AmbassadorDoge/notakeeb/PCB/marbastlib-main/resources/repolist.png

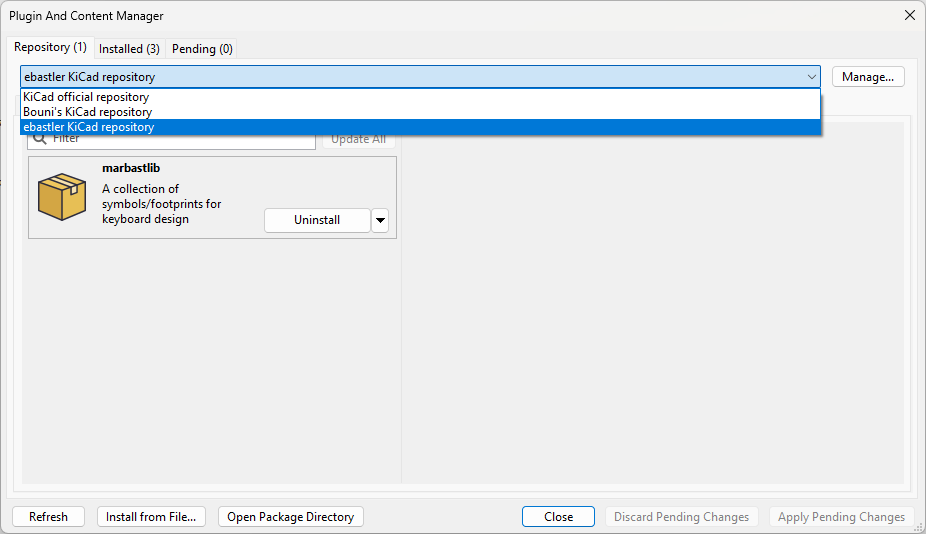
PCB/marbastlib-main/resources/repolist.png
