AmbassadorDoge/notakeeb/PCB/scottokeebs-main/Extras/ScottoModules/STM32F072CBT6/meta/matrix.png

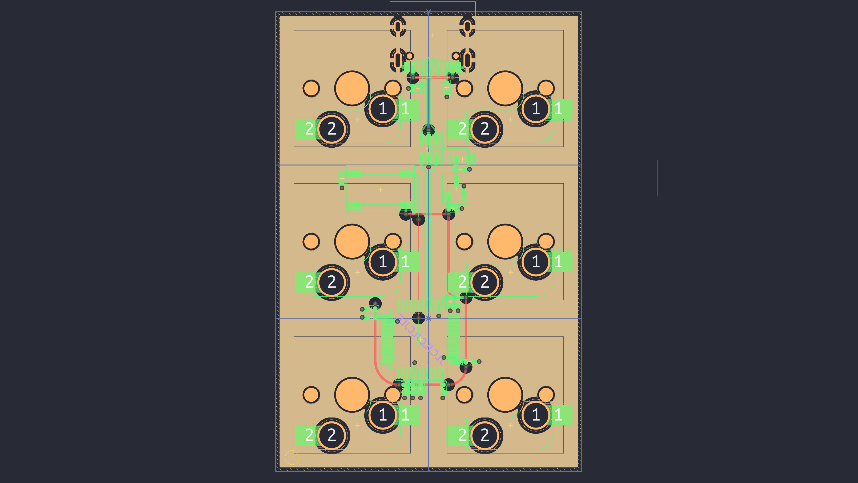
PCB/scottokeebs-main/Extras/ScottoModules/STM32F072CBT6/meta/matrix.png
