AmbassadorDoge/notakeeb/PCB/scottokeebs-main/Extras/ScottoModules/STM32F072CBT6/meta/scottomodules.png

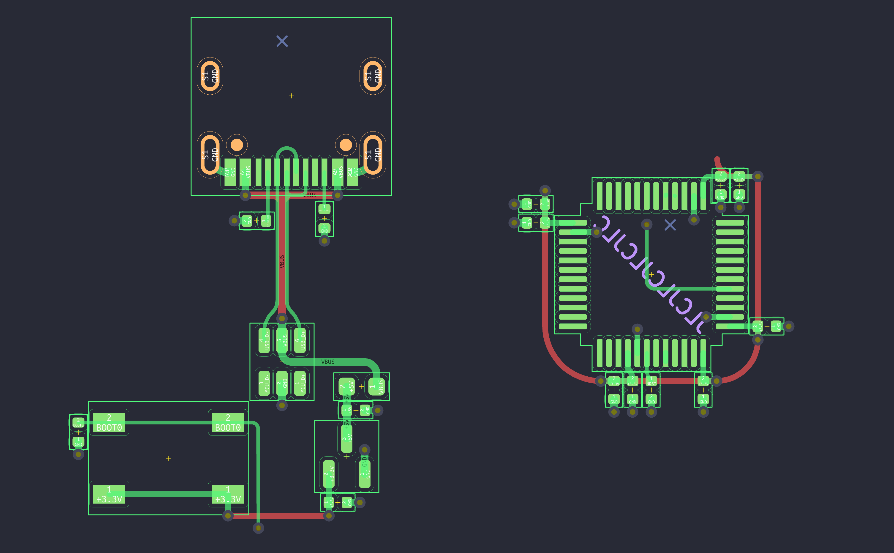
PCB/scottokeebs-main/Extras/ScottoModules/STM32F072CBT6/meta/scottomodules.png
