AmbassadorDoge/notakeeb/PCB/scottokeebs-main/ScottoFrog/Firmware/scottofrog.jpg

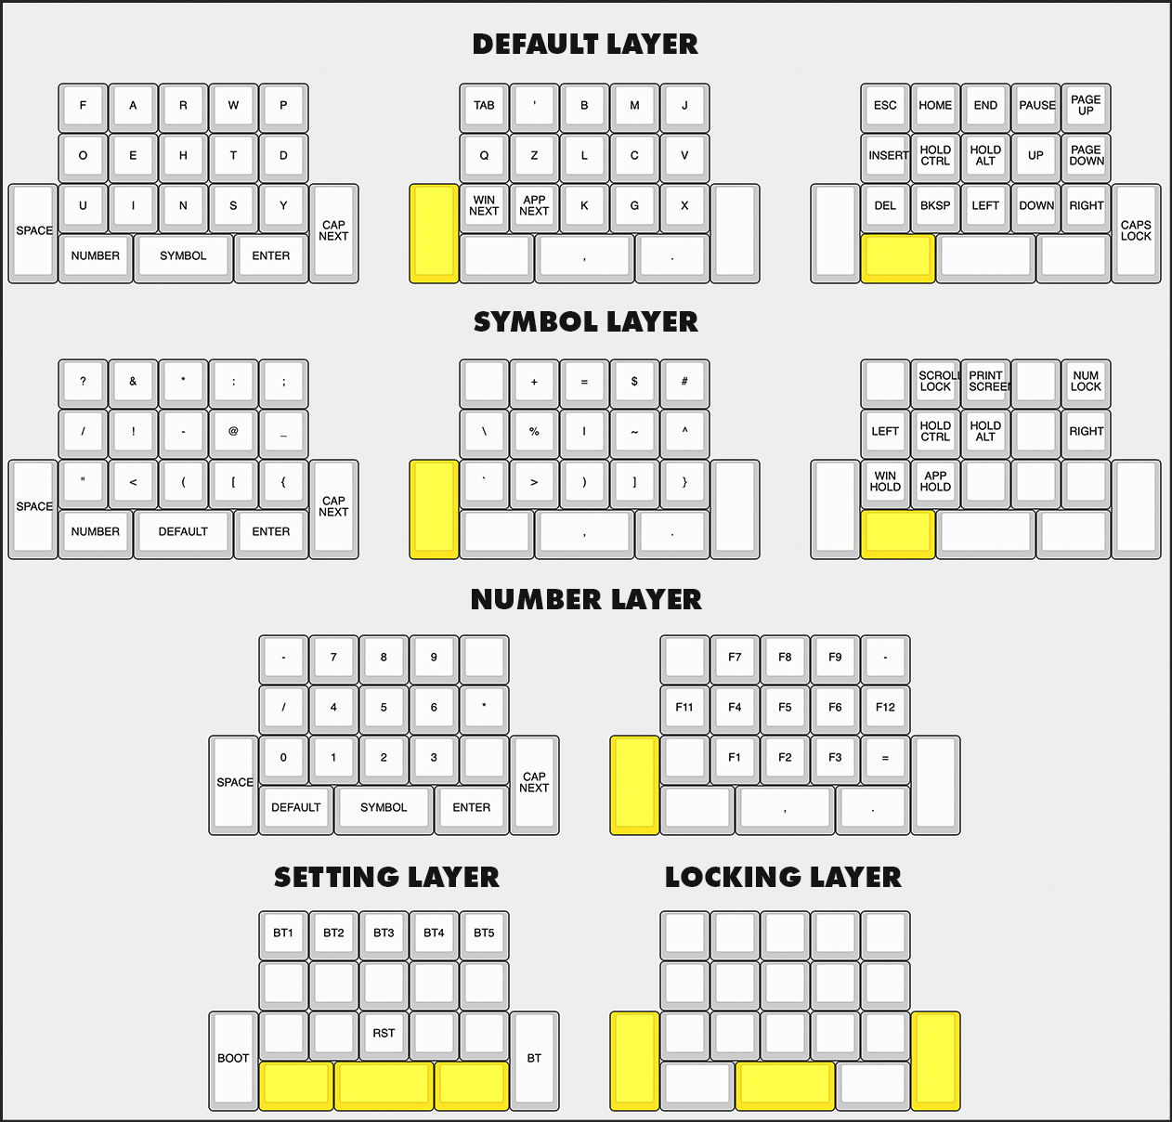
PCB/scottokeebs-main/ScottoFrog/Firmware/scottofrog.jpg
