AmbassadorDoge/notakeeb/PCB/scottokeebs-main/Extras/ScottoCaps/Flat/Legends/Asterisk.3mf

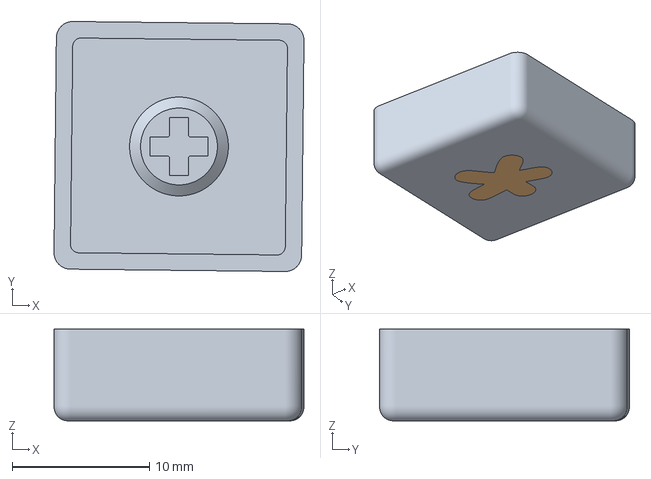
[picture p15: CAD file, 2025-07-04]
PCB/scottokeebs-main/Extras/ScottoCaps/Flat/Legends/Asterisk.3mf
18.2 x 18.2 x 6.70 mm
Asterisk_Keycap
Asterisk_Text
