AmbassadorDoge/notakeeb/PCB/scottokeebs-main/Extras/ScottoCaps/Scooped/Choc/Legends/16x16/Hexagon (16x16).3mf

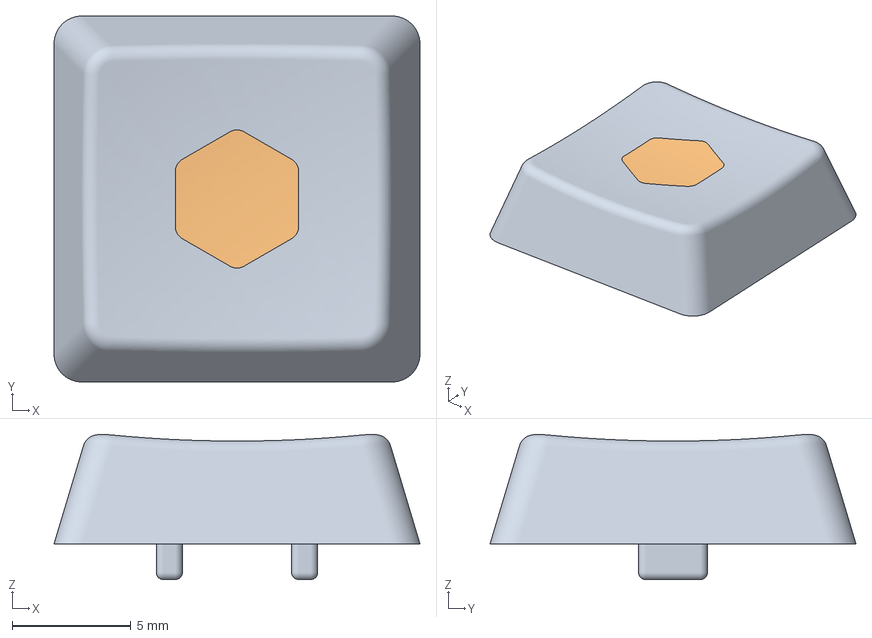
[picture p16: CAD file, 2025-07-04]
PCB/scottokeebs-main/Extras/ScottoCaps/Scooped/Choc/Legends/16x16/Hexagon (16x16).3mf
15.4 x 15.4 x 6.11 mm
Keycap
Legend
