AmbassadorDoge/notakeeb/PCB/scottokeebs-main/Extras/ScottoCaps/Scooped/Choc/Legends/18x18/U (18x18).3mf

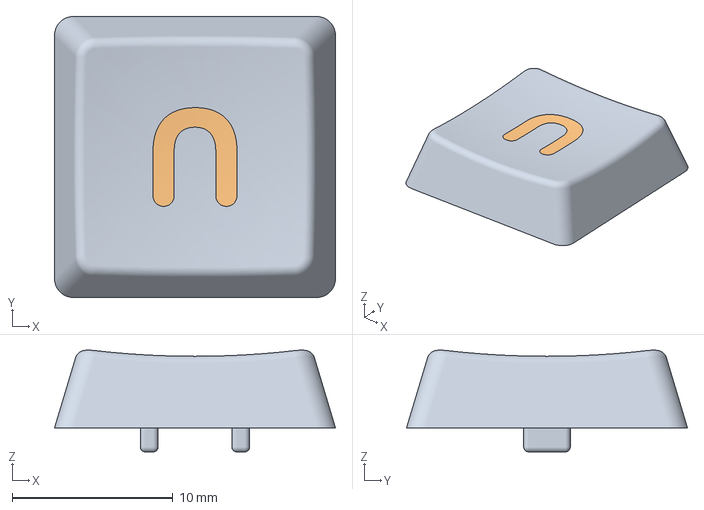
[picture p18: CAD file, 2025-07-04]
PCB/scottokeebs-main/Extras/ScottoCaps/Scooped/Choc/Legends/18x18/U (18x18).3mf
17.5 x 17.5 x 6.33 mm
Keycap
Legend
