AmbassadorDoge/notakeeb/PCB/scottokeebs-main/Extras/ScottoCaps/Scooped/MX/Legends/D.3mf

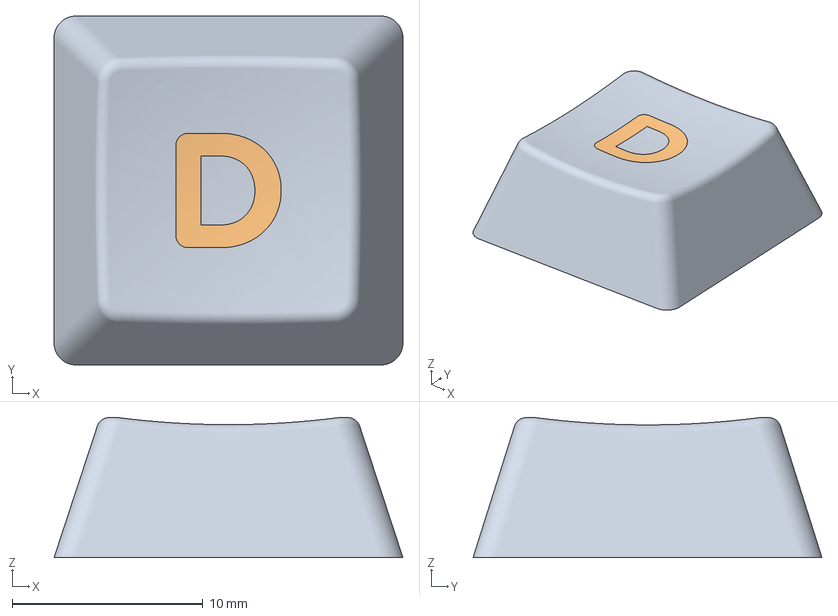
[picture p19: CAD file, 2025-07-04]
PCB/scottokeebs-main/Extras/ScottoCaps/Scooped/MX/Legends/D.3mf
18.3 x 18.3 x 7.36 mm
Keycap
Legend
