AmbassadorDoge/notakeeb/PCB/scottokeebs-main/Extras/ScottoCaps/Scooped/Choc/Legends/18x17/Double Quotes (18x17).3mf

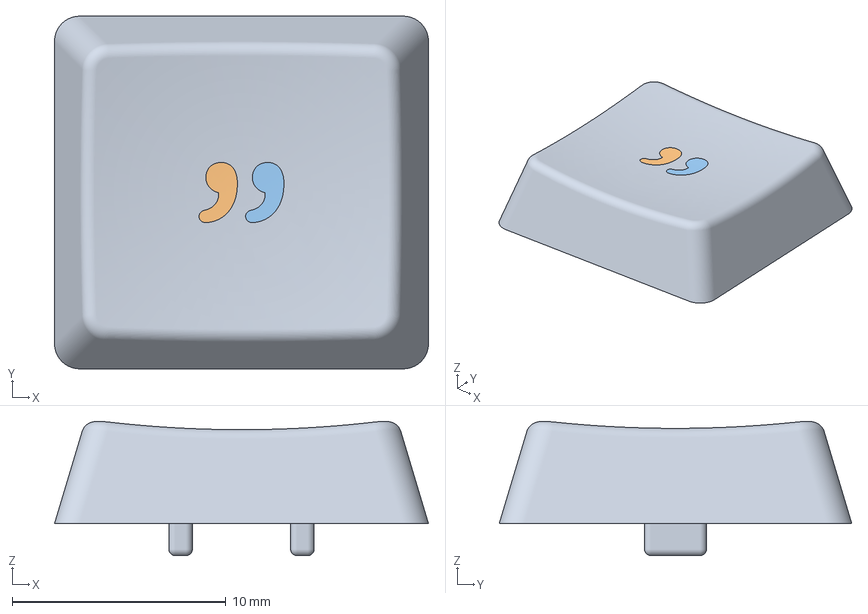
[picture p20: CAD file, 2025-07-04]
PCB/scottokeebs-main/Extras/ScottoCaps/Scooped/Choc/Legends/18x17/Double Quotes (18x17).3mf
17.5 x 16.5 x 6.28 mm
Keycap
